wiciu15/NRF51_CAN_BLE_HID_Multimedia/inc/hid_mmkeys.h

//HID report key offsets in second byte

#define MEDIA_MUTE 		0
#define MEDIA_VOLUP 	1
#define MEDIA_VOLDOWN 	2
#define MEDIA_PLAY 		3
#define MEDIA_STOP 		4
#define MEDIA_PREV 		5
#define MEDIA_NEXT 		6

//CAN frame data coming from can-id 0x10438040 depending on steering wheel key pressed
#define CAN_MEDIA_ALL_RELEASED 		0x00
#define CAN_MEDIA_NEXT 				0x03
#define CAN_MEDIA_PREV 				0x04
#define CAN_MEDIA_MUTE				0x07
